m-xor/Thermometer_hardware/photos/fit_bottom.JPG

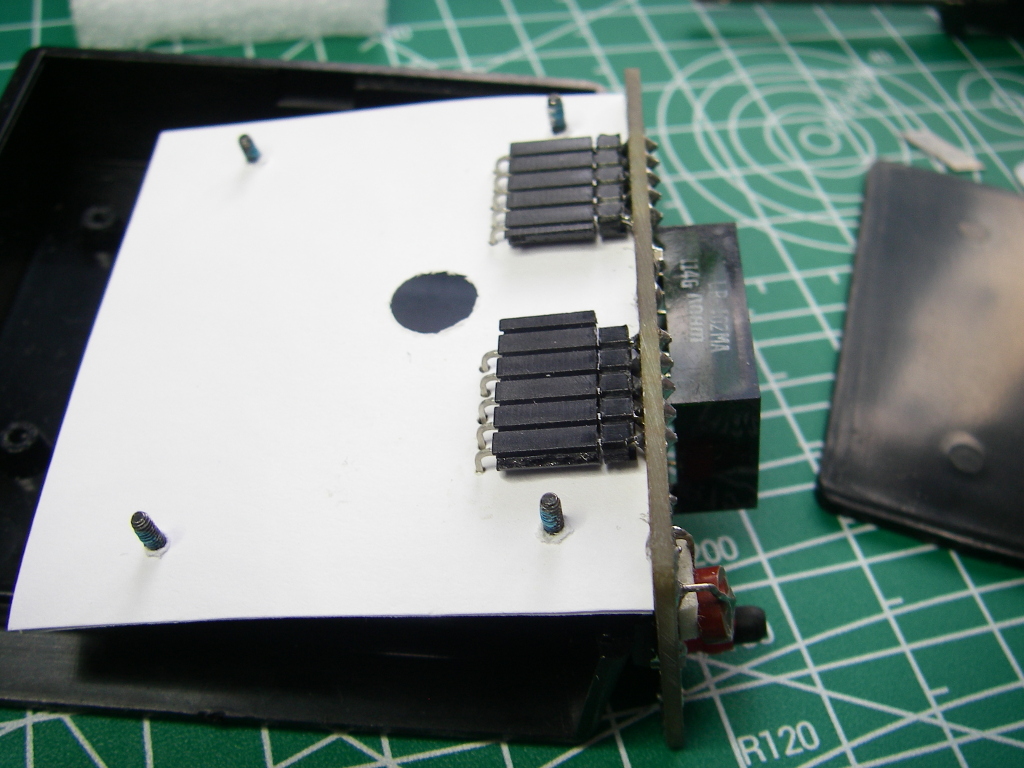
photos/fit_bottom.JPG
