m-xor/Thermometer_hardware/photos/fit_front.JPG

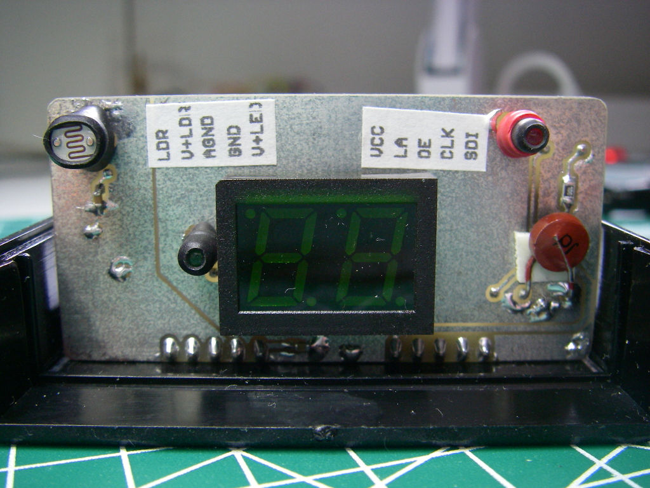
photos/fit_front.JPG
