m-xor/Thermometer_hardware/photos/fit_side.JPG

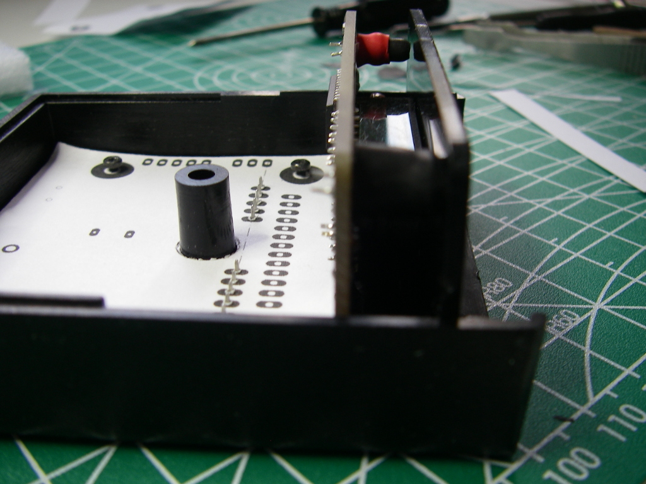
photos/fit_side.JPG
