m-xor/Thermometer_hardware/photos/fit_top.JPG

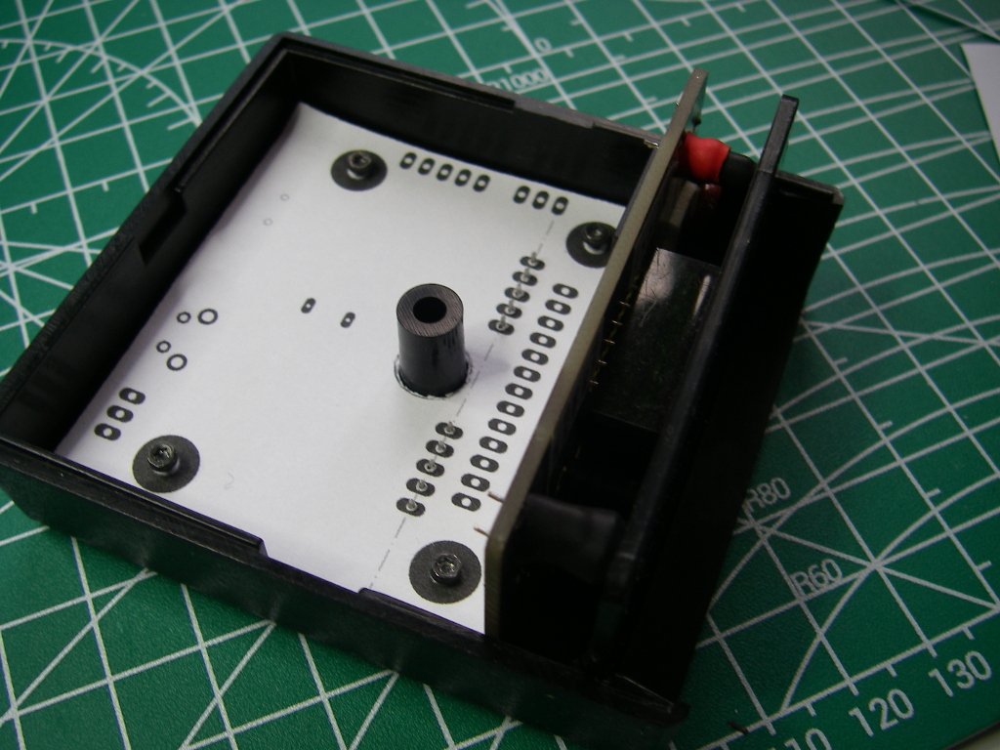
photos/fit_top.JPG
