m-xor/Thermometer_hardware/photos/IMGP1740.JPG

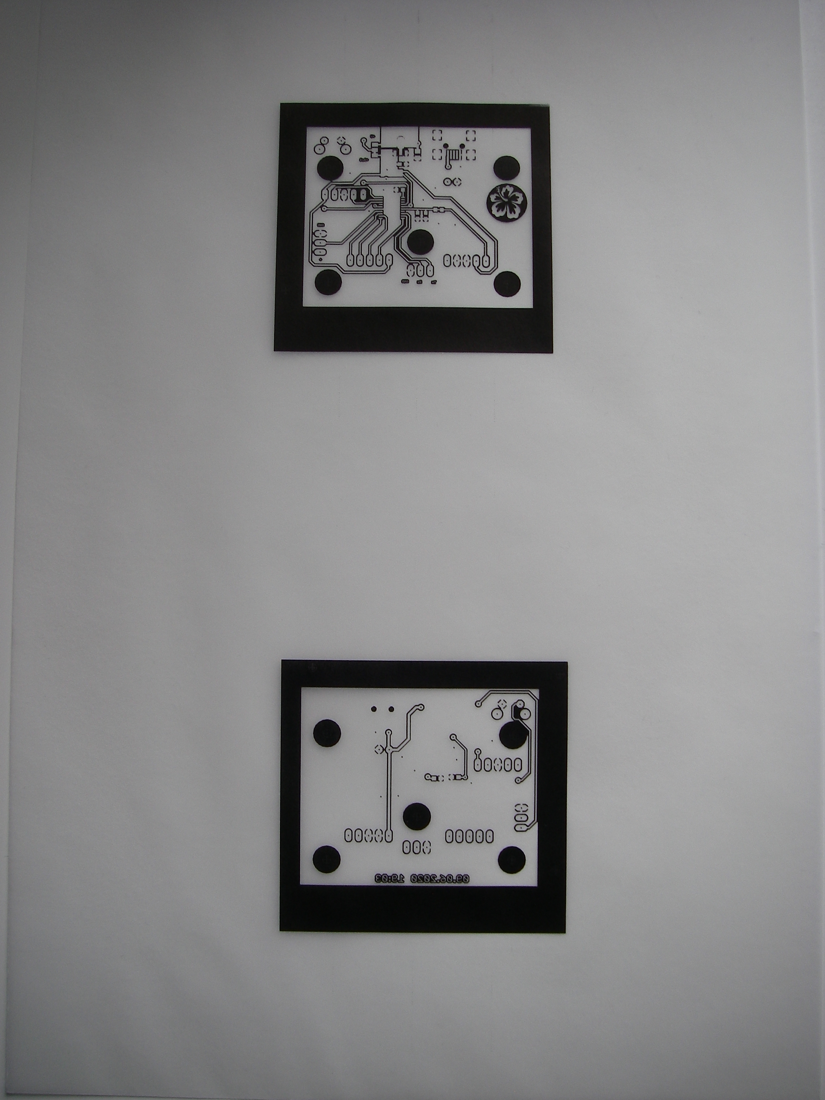
photos/IMGP1740.JPG
