m-xor/Thermometer_hardware/photos/IMGP1743.JPG

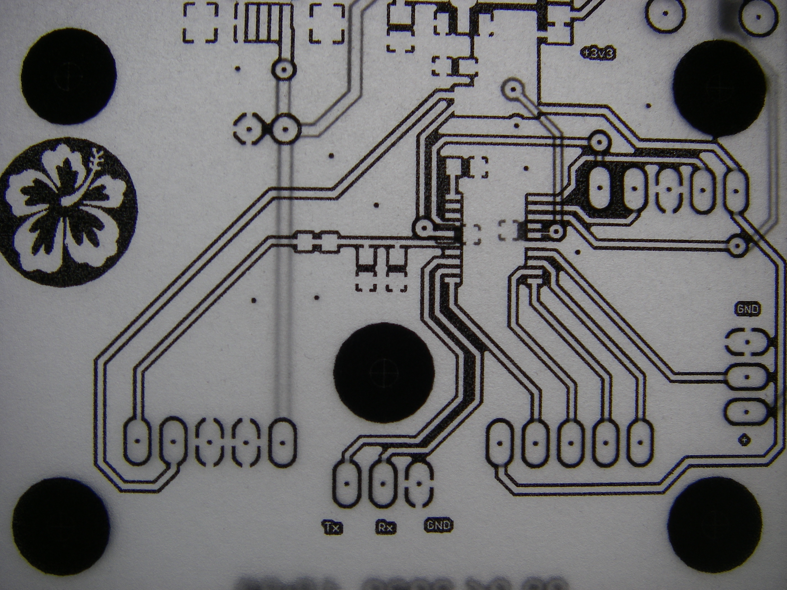
photos/IMGP1743.JPG
