m-xor/Thermometer_hardware/photos/IMGP1746.JPG

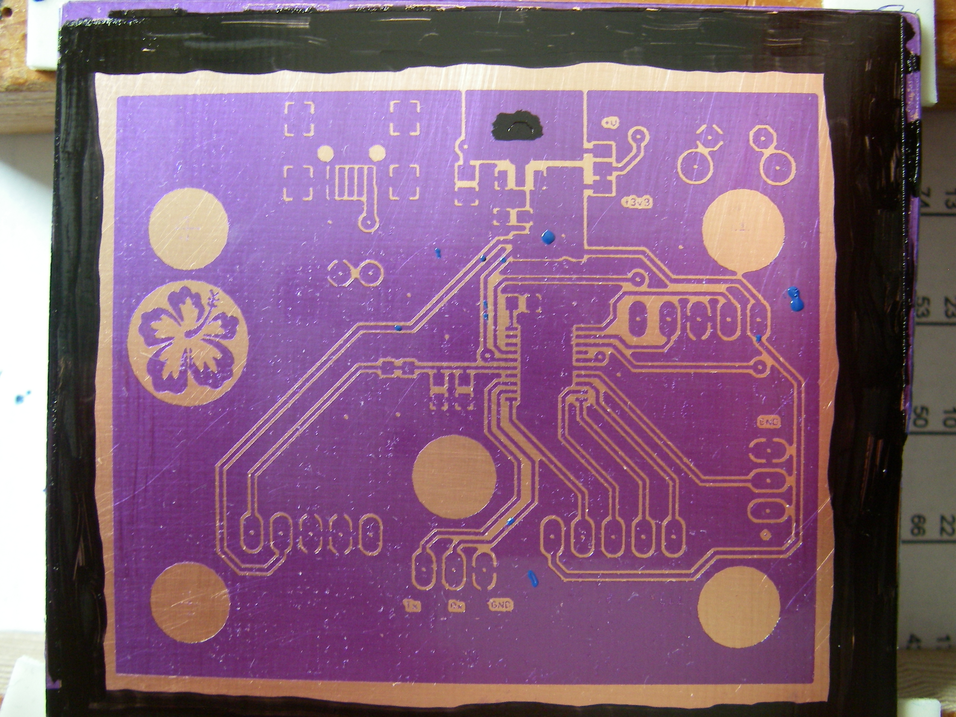
photos/IMGP1746.JPG
