m-xor/Thermometer_hardware/photos/IMGP1752.JPG

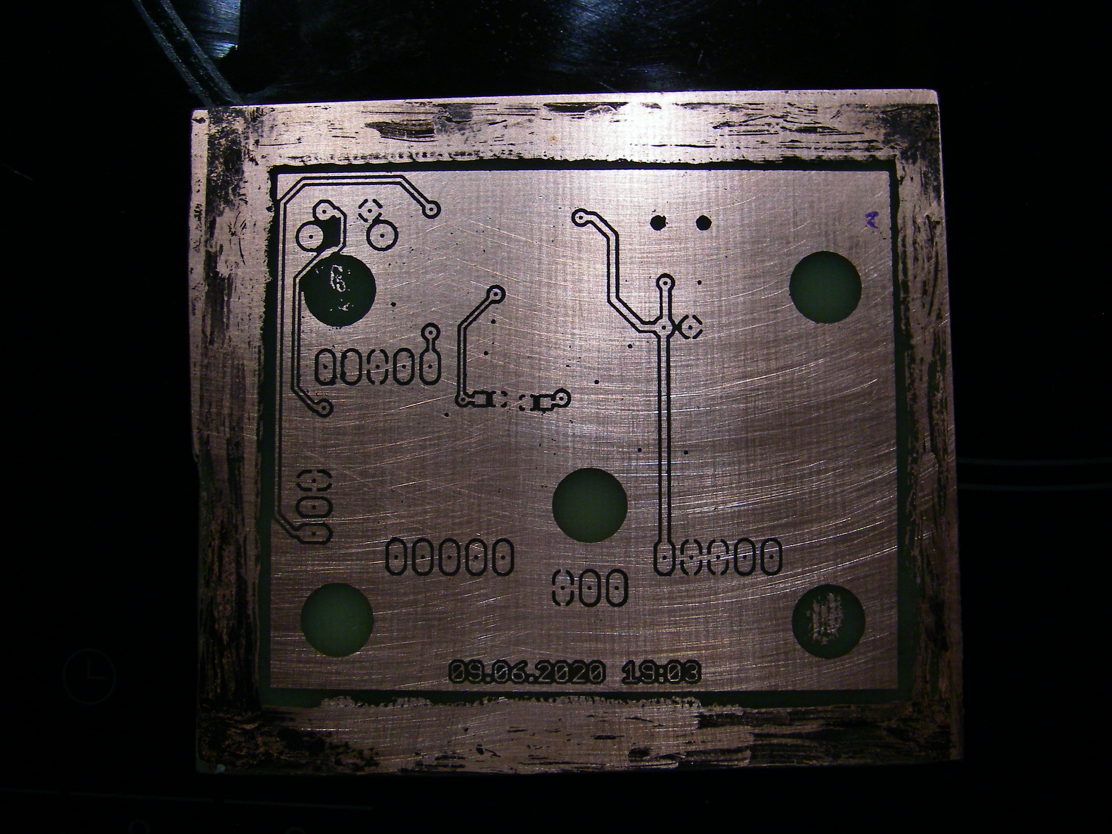
photos/IMGP1752.JPG
