m-xor/Thermometer_hardware/photos/IMGP1754.JPG

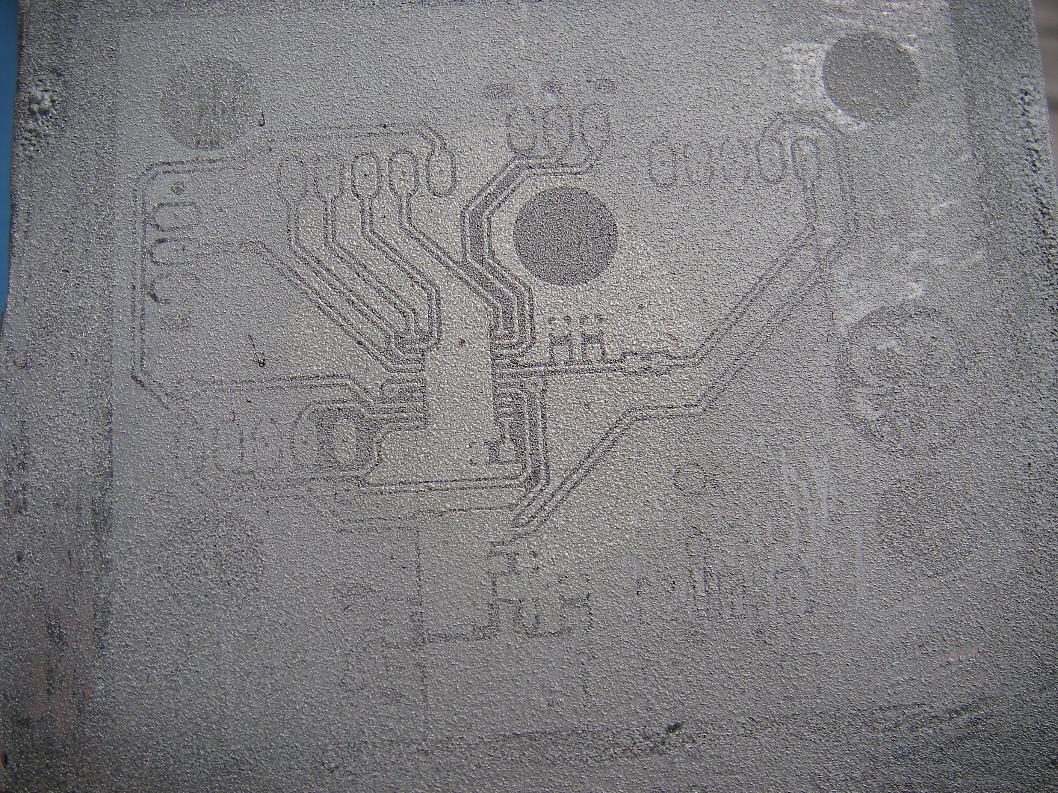
photos/IMGP1754.JPG
