m-xor/Thermometer_hardware/photos/IMGP1756.JPG

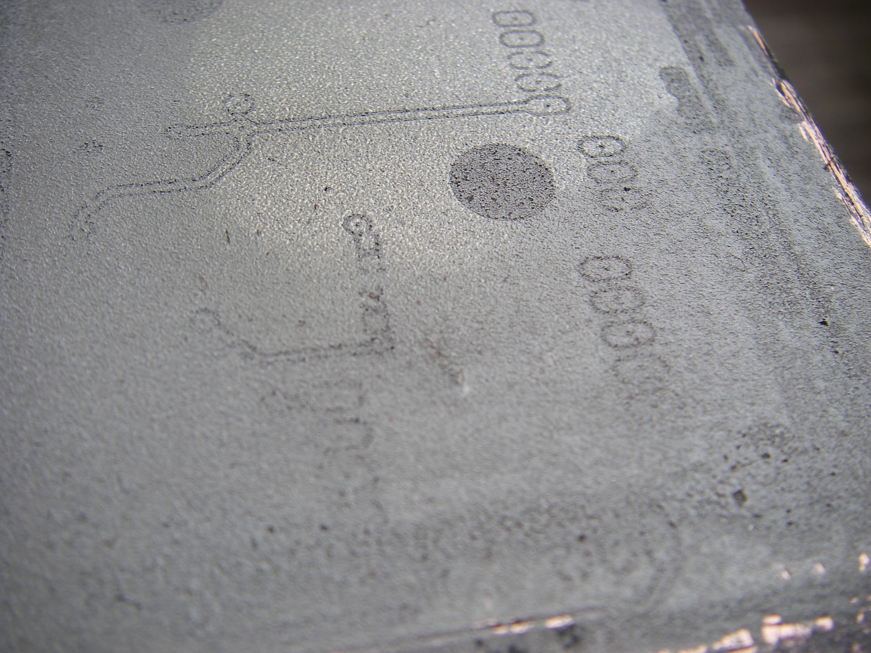
photos/IMGP1756.JPG
