m-xor/Thermometer_hardware/photos/IMGP1758.JPG

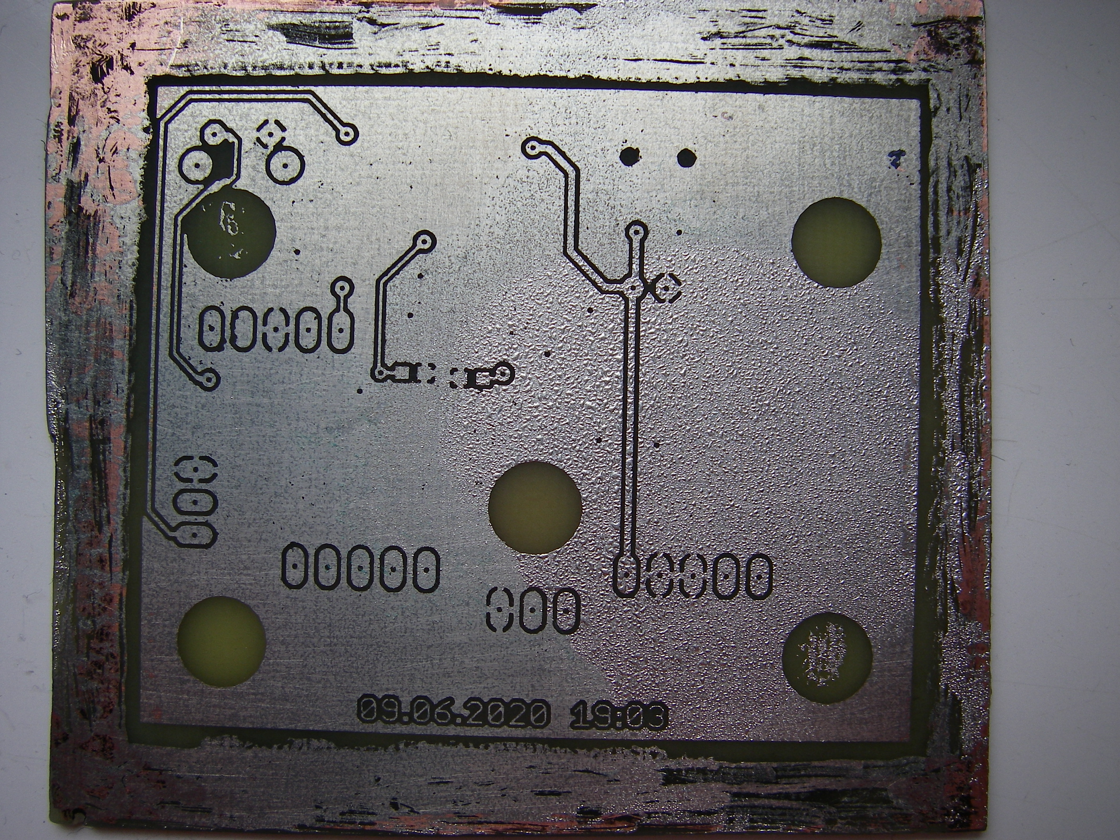
photos/IMGP1758.JPG
