m-xor/Thermometer_hardware/photos/IMGP1760.JPG

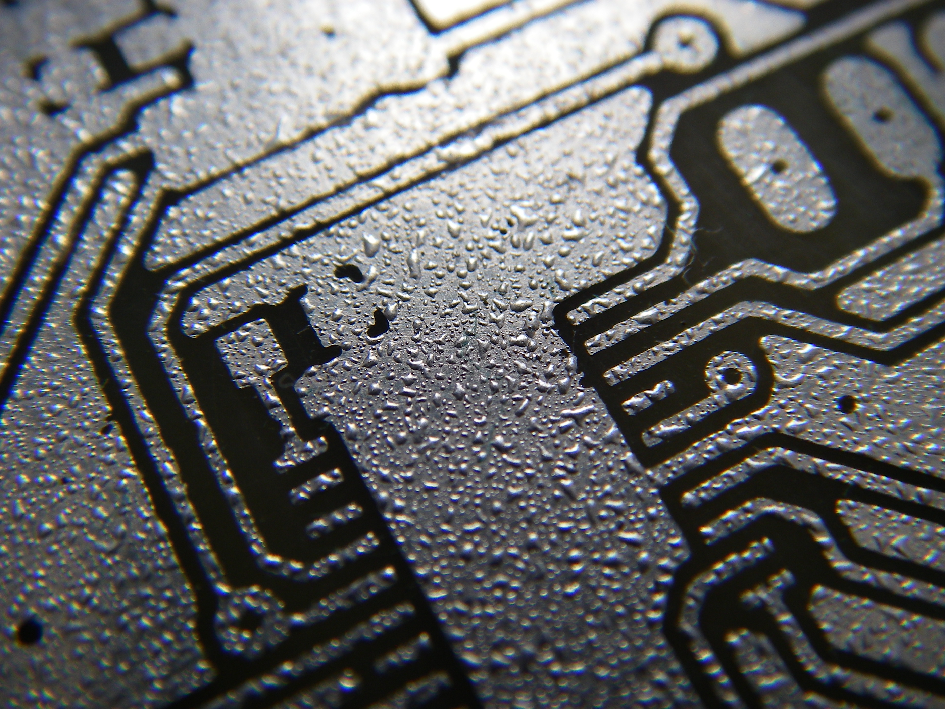
photos/IMGP1760.JPG
