m-xor/Thermometer_hardware/photos/IMGP1763.JPG

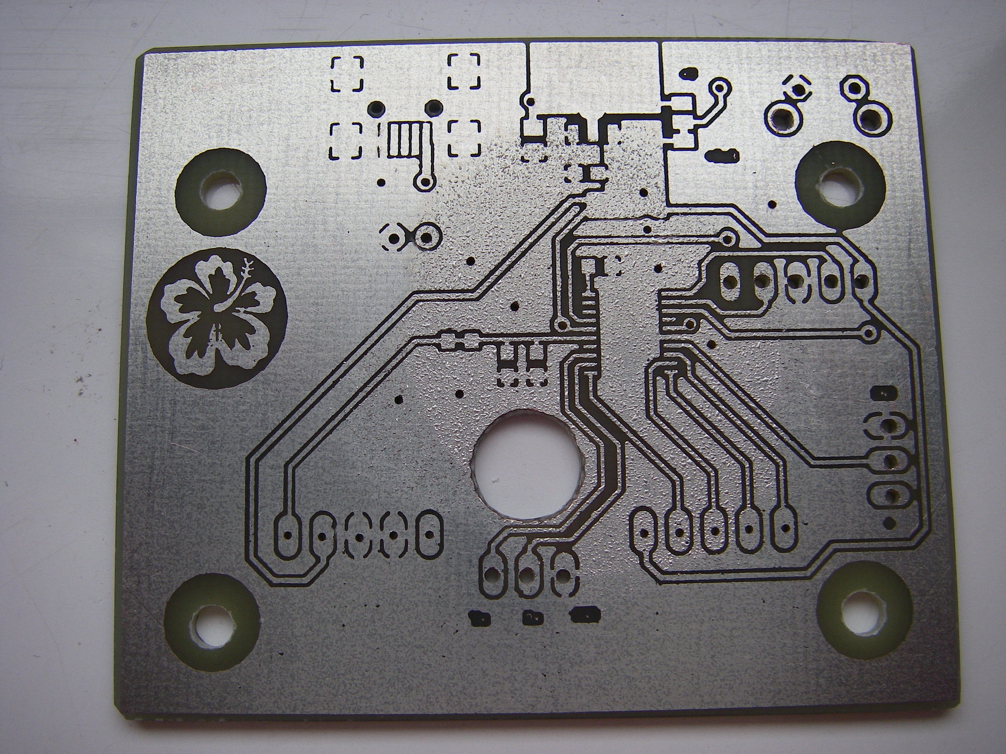
photos/IMGP1763.JPG
