m-xor/Thermometer_hardware/photos/IMGP1764.JPG

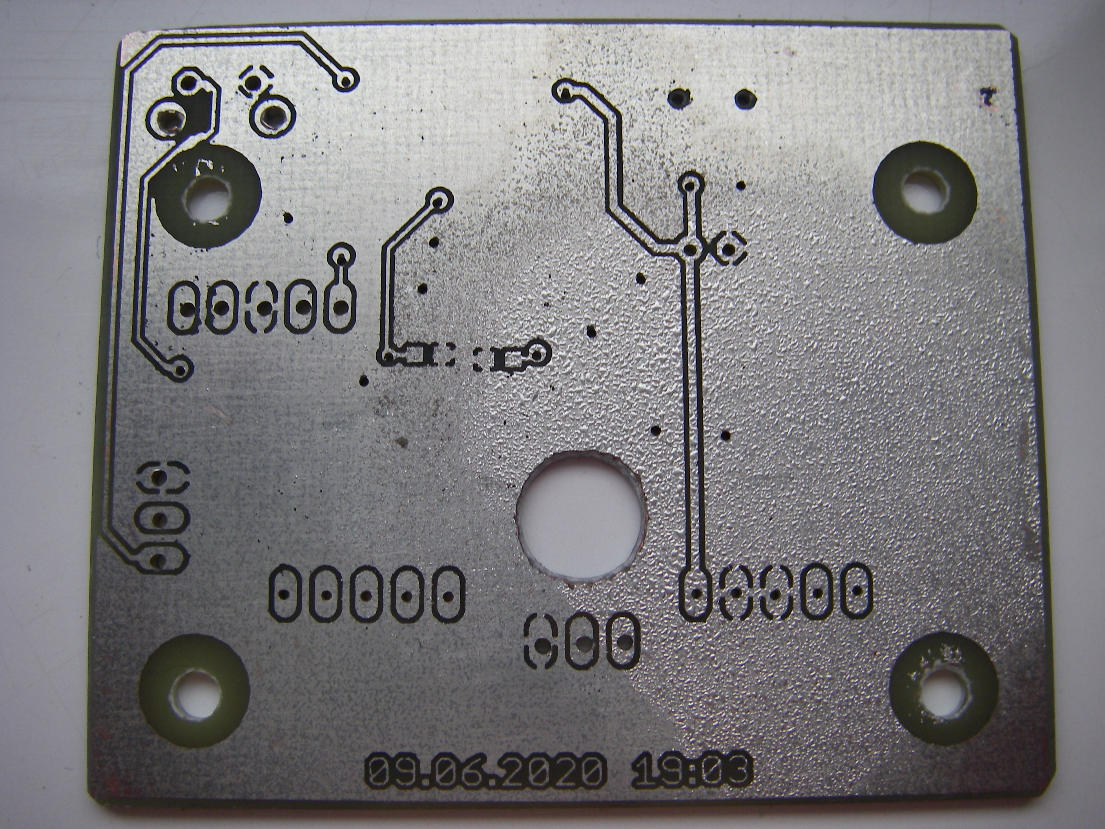
photos/IMGP1764.JPG
