m-xor/Thermometer_hardware/photos/IMGP1765.JPG

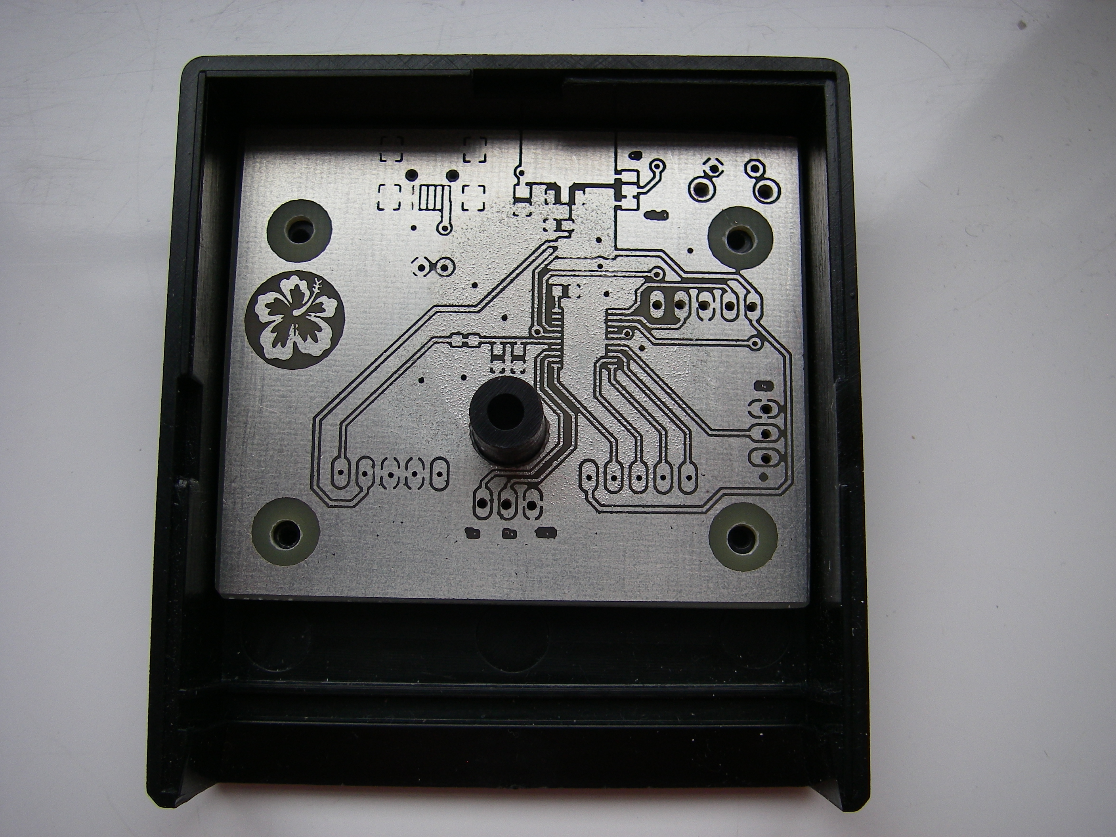
photos/IMGP1765.JPG
