m-xor/Thermometer_hardware/photos/IMGP1773.JPG

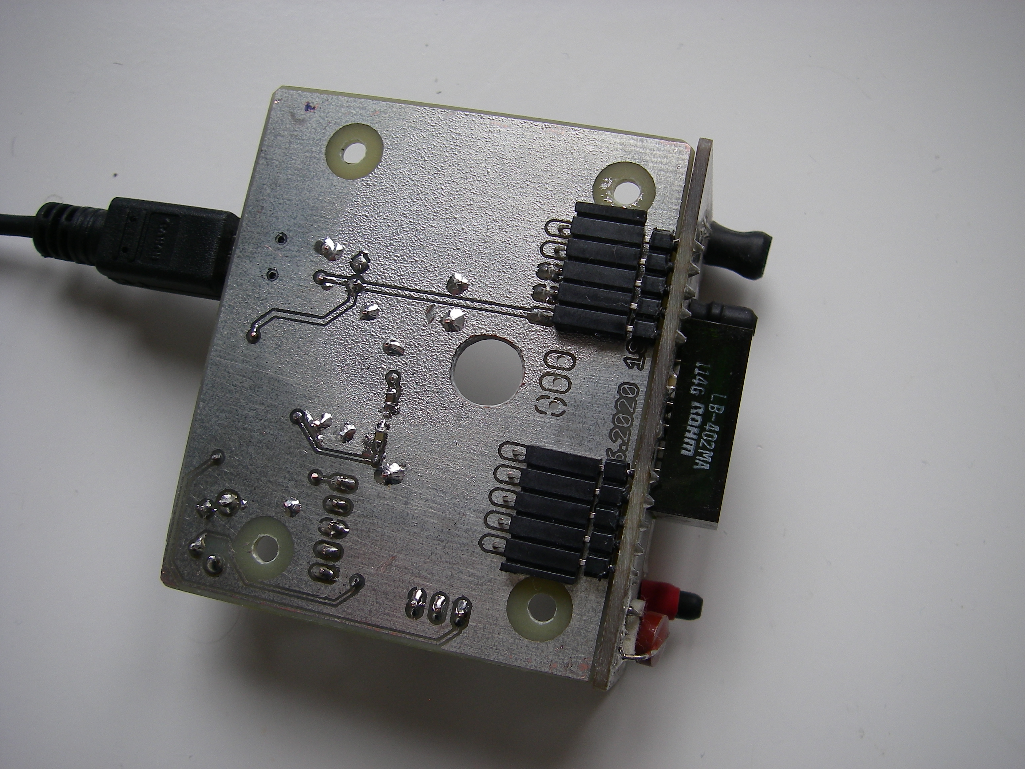
photos/IMGP1773.JPG
