m-xor/Thermometer_hardware/photos/IMGP1774.JPG

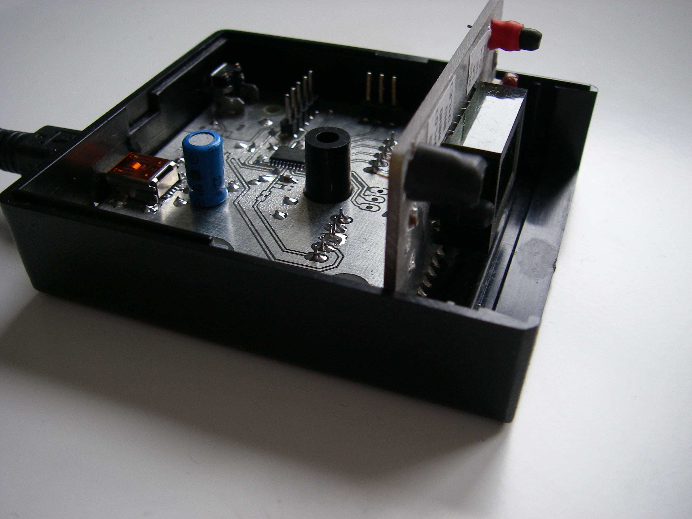
photos/IMGP1774.JPG
