m-xor/Thermometer_hardware/photos/IMGP1777.JPG

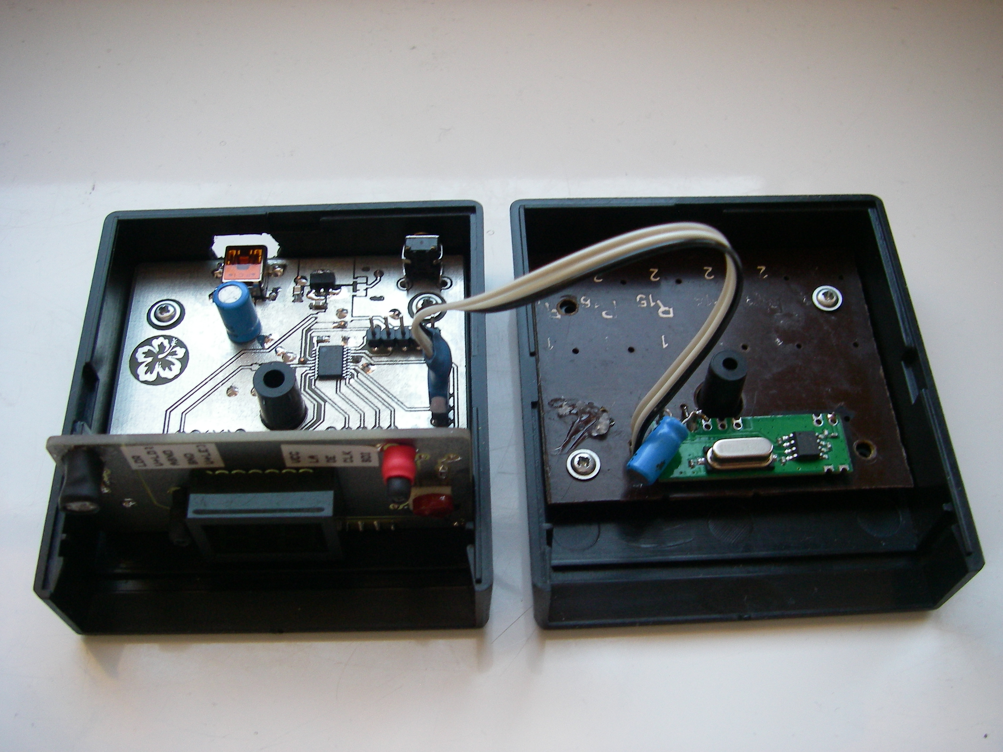
photos/IMGP1777.JPG
