m-xor/Thermometer_hardware/photos/IMGP1779.JPG

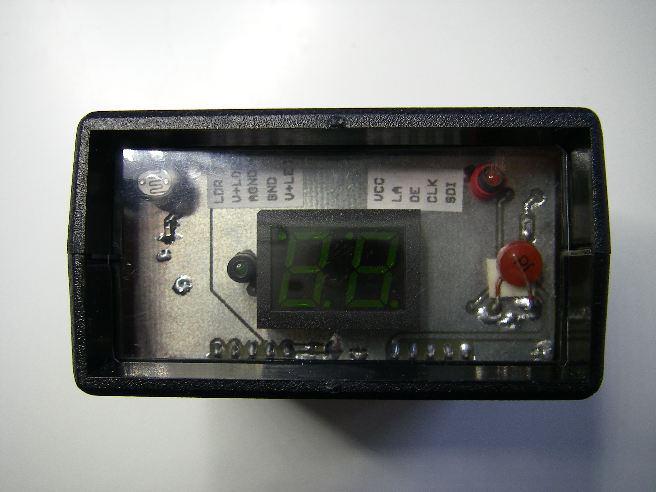
photos/IMGP1779.JPG
