m-xor/Thermometer_hardware/photos/IMGP1780.JPG

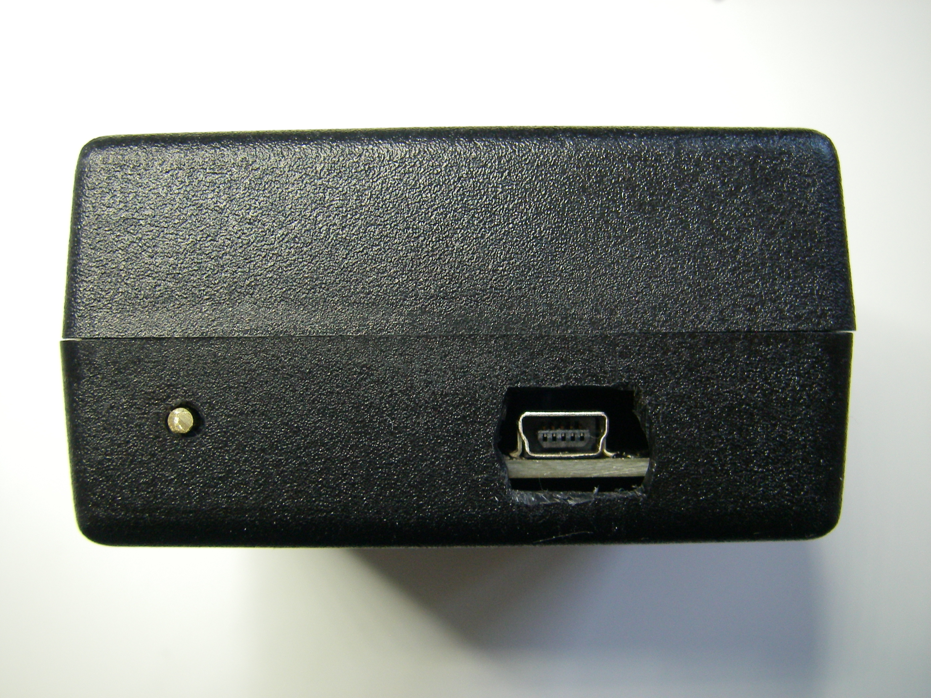
photos/IMGP1780.JPG
