m-xor/Thermometer_hardware/photos/template.JPG

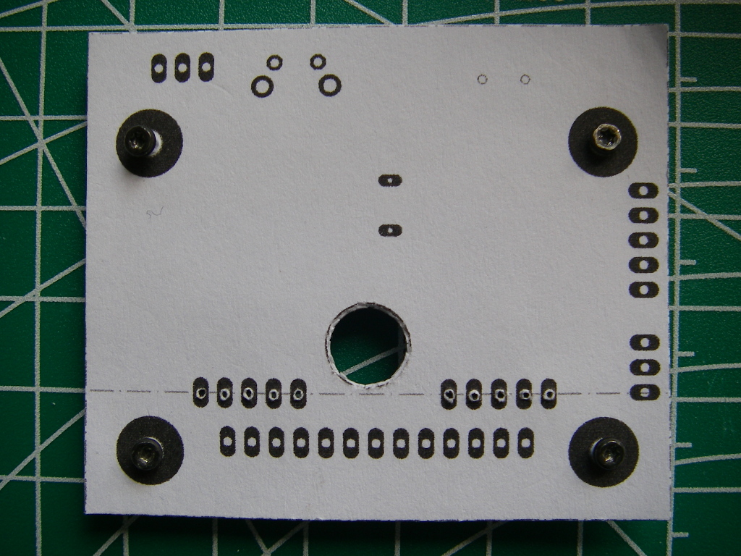
photos/template.JPG
