m-xor/Thermometer_hardware/photos/test_circuit.JPG

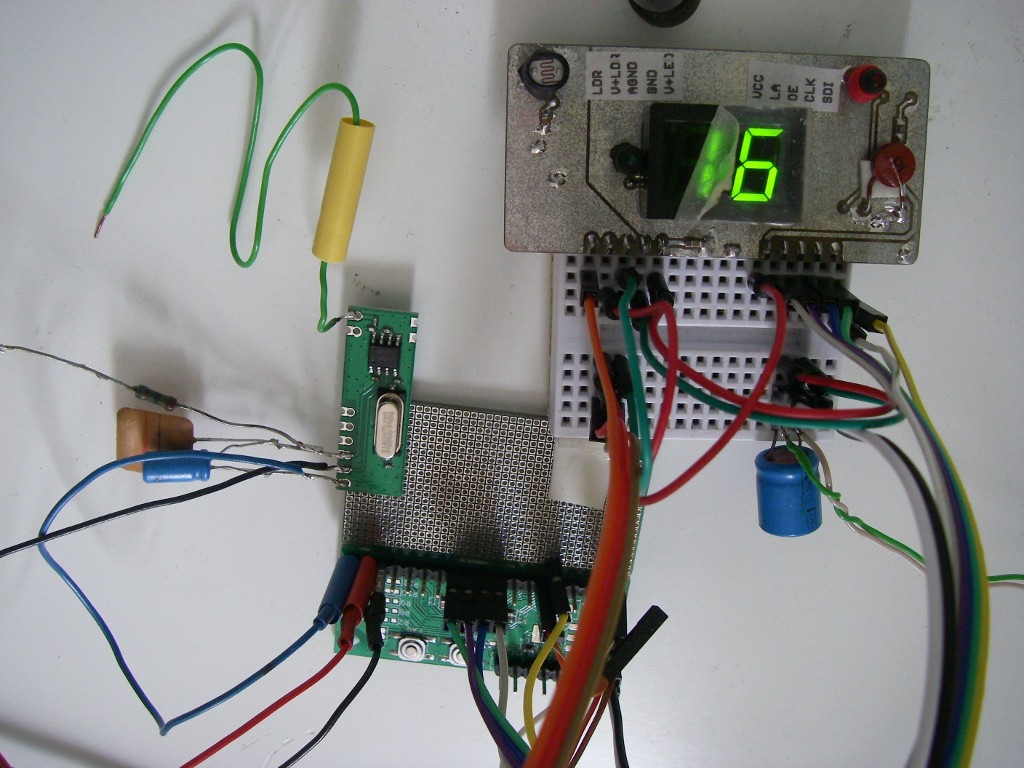
photos/test_circuit.JPG
